njeff/powerglove/fw/powerglove_fw/drivers/drv2605l.c

/*!
 * @file Adafruit_DRV2605.cpp
 *
 * @mainpage Adafruit DRV2605L Haptic Driver
 *
 * @section intro_sec Introduction
 *
 * This is a library for the Adafruit DRV2605L Haptic Driver ---->
 * http://www.adafruit.com/products/2305
 *
 * Check out the links above for our tutorials and wiring diagrams.
 *
 * This motor/haptic driver uses I2C to communicate.
 *
 * Adafruit invests time and resources providing this open source code,
 * please support Adafruit and open-source hardware by purchasing
 * products from Adafruit!
 *
 * @section author Author
 *
 * Written by Limor Fried/Ladyada for Adafruit Industries.
 *
 * @section license License
 *
 * MIT license, all text above must be included in any redistribution.
 *
 */

// Adapted to NRF

#include <stdbool.h>
#include <stdint.h>

#include "app_error.h"
#include "nrf.h"
#include "nrf_delay.h"
#include "nrf_twi_mngr.h"
#include "nrf_drv_timer.h"

#include "drv2605l.h"


const nrf_twi_mngr_t * i2c_dev; 

static void i2c_read_bytes(uint8_t i2c_addr, uint8_t reg_addr, uint8_t* data, uint8_t len) {
  nrf_twi_mngr_transfer_t const read_transfer[] = {
    NRF_TWI_MNGR_WRITE(i2c_addr, &reg_addr, 1, NRF_TWI_MNGR_NO_STOP),
    NRF_TWI_MNGR_READ(i2c_addr, data, len, 0),
  };
  ret_code_t error_code = nrf_twi_mngr_perform(i2c_dev, NULL, read_transfer, 2, NULL);
  APP_ERROR_CHECK(error_code);
}

static uint8_t i2c_reg_read(uint8_t i2c_addr, uint8_t reg_addr) {
  uint8_t rx_buf = 0;
  nrf_twi_mngr_transfer_t const read_transfer[] = {
    NRF_TWI_MNGR_WRITE(i2c_addr, &reg_addr, 1, NRF_TWI_MNGR_NO_STOP),
    NRF_TWI_MNGR_READ(i2c_addr, &rx_buf, 1, 0),
  };
  ret_code_t error_code = nrf_twi_mngr_perform(i2c_dev, NULL, read_transfer, 2, NULL);
  APP_ERROR_CHECK(error_code);
  return rx_buf;
}

static void i2c_reg_write(uint8_t i2c_addr, uint8_t reg_addr, uint8_t data) {
  uint8_t buf[2] = {reg_addr, data};
  nrf_twi_mngr_transfer_t const write_transfer[] = {
    NRF_TWI_MNGR_WRITE(i2c_addr, buf, 2, 0),
  };
  ret_code_t error_code = nrf_twi_mngr_perform(i2c_dev, NULL, write_transfer, 1, NULL);
  APP_ERROR_CHECK(error_code);
}

static void writeRegister8(uint8_t reg, uint8_t val) {
	i2c_reg_write(DRV2605_ADDR, reg, val);
}

static uint8_t readRegister8(uint8_t reg) {
	return i2c_reg_read(DRV2605_ADDR, reg);
}


/**************************************************************************/
/*!
  @brief  Setup the HW
  @return Always true
*/
/**************************************************************************/
bool initDRV2605(const nrf_twi_mngr_t* i2c) {
  i2c_dev = i2c;

  writeRegister8(DRV2605_REG_MODE, 0x00); // out of standby

  writeRegister8(DRV2605_REG_RTPIN, 0x00); // no real-time-playback

  writeRegister8(DRV2605_REG_WAVESEQ1, 1); // strong click
  writeRegister8(DRV2605_REG_WAVESEQ2, 0); // end sequence

  writeRegister8(DRV2605_REG_OVERDRIVE, 0); // no overdrive

  writeRegister8(DRV2605_REG_SUSTAINPOS, 0);
  writeRegister8(DRV2605_REG_SUSTAINNEG, 0);
  writeRegister8(DRV2605_REG_BREAK, 0);
  writeRegister8(DRV2605_REG_AUDIOMAX, 0x64);

  // ERM open loop

  // turn off N_ERM_LRA
  writeRegister8(DRV2605_REG_FEEDBACK,
                 readRegister8(DRV2605_REG_FEEDBACK) & 0x7F);
  // turn on ERM_OPEN_LOOP
  writeRegister8(DRV2605_REG_CONTROL3,
                 readRegister8(DRV2605_REG_CONTROL3) | 0x20);

  return true;
}

/**************************************************************************/
/*!
  @brief Select the haptic waveform to use.
  @param slot The waveform slot to set, from 0 to 7
  @param w The waveform sequence value, refers to an index in the ROM library.
    Playback starts at slot 0 and continues through to slot 7, stopping if it
  encounters a value of 0. A list of available waveforms can be found in
  section 11.2 of the datasheet: http://www.adafruit.com/datasheets/DRV2605.pdf
*/
/**************************************************************************/
void DRV2605_setWaveform(uint8_t slot, uint8_t w) {
  writeRegister8(DRV2605_REG_WAVESEQ1 + slot, w);
}

/**************************************************************************/
/*!
  @brief Select the waveform library to use.
  @param lib Library to use, 0 = Empty, 1-5 are ERM, 6 is LRA.
    See section 7.6.4 in the datasheet for more details:
  http://www.adafruit.com/datasheets/DRV2605.pdf
*/
/**************************************************************************/
void DRV2605_selectLibrary(uint8_t lib) {
  writeRegister8(DRV2605_REG_LIBRARY, lib);
}

/**************************************************************************/
/*!
  @brief Start playback of the waveforms (start moving!).
*/
/**************************************************************************/
void DRV2605_go() { writeRegister8(DRV2605_REG_GO, 1); }

/**************************************************************************/
/*!
  @brief Stop playback.
*/
/**************************************************************************/
void DRV2605_stop() { writeRegister8(DRV2605_REG_GO, 0); }

/**************************************************************************/
/*!
  @brief Set the device mode.
  @param mode Mode value, see datasheet section 7.6.2:
  http://www.adafruit.com/datasheets/DRV2605.pdf
    0: Internal trigger, call go() to start playback\n
    1: External trigger, rising edge on IN pin starts playback\n
    2: External trigger, playback follows the state of IN pin\n
    3: PWM/analog input\n
    4: Audio\n
    5: Real-time playback\n
    6: Diagnostics\n
    7: Auto calibration
*/
/**************************************************************************/
void DRV2605_setMode(uint8_t mode) {
  writeRegister8(DRV2605_REG_MODE, mode);
}

/**************************************************************************/
/*!
  @brief Set the realtime value when in RTP mode, used to directly drive the
  haptic motor.
  @param rtp 8-bit drive value.
*/
/**************************************************************************/
void DRV2605_setRealtimeValue(uint8_t rtp) {
  writeRegister8(DRV2605_REG_RTPIN, rtp);
}

/**************************************************************************/
/*!
  @brief Use ERM (Eccentric Rotating Mass) mode.
*/
/**************************************************************************/
void DRV2605_useERM() {
  writeRegister8(DRV2605_REG_FEEDBACK,
                 readRegister8(DRV2605_REG_FEEDBACK) & 0x7F);
}

/**************************************************************************/
/*!
  @brief Use LRA (Linear Resonance Actuator) mode.
*/
/**************************************************************************/
void DRV2605_useLRA() {
  writeRegister8(DRV2605_REG_FEEDBACK,
                 readRegister8(DRV2605_REG_FEEDBACK) | 0x80);
}
